hobbyiot/HELIUM-SENSORS/H2S-Dev V1.2/SW/H2S-CFG-YOUR_DEVBOARD.h

// *** 
// Definitions for H2S device

// MUST BE LSB!!!
#define H2S_DEVEUI 0xpp, 0xpp, 0xpp, 0xpp, 0xpp, 0xpp, 0xpp, 0xpp

// MUST BE LSB!!!
#define H2S_APPEUI 0xpp, 0xpp, 0xpp, 0xpp, 0xpp, 0xpp, 0xpp, 0xpp

// MUST BE MSB!!!
#define H2S_APPKEY 0xpp, 0xpp, 0xpp, 0xpp, 0xpp, 0xpp, 0xpp, 0xpp, 0xpp, 0xpp, 0xpp, 0xpp, 0xpp, 0xpp, 0xpp, 0xpp
